BPBorer/RGB2XGA/PCB/RGB2VGA/Manu/3v3 - Err.png

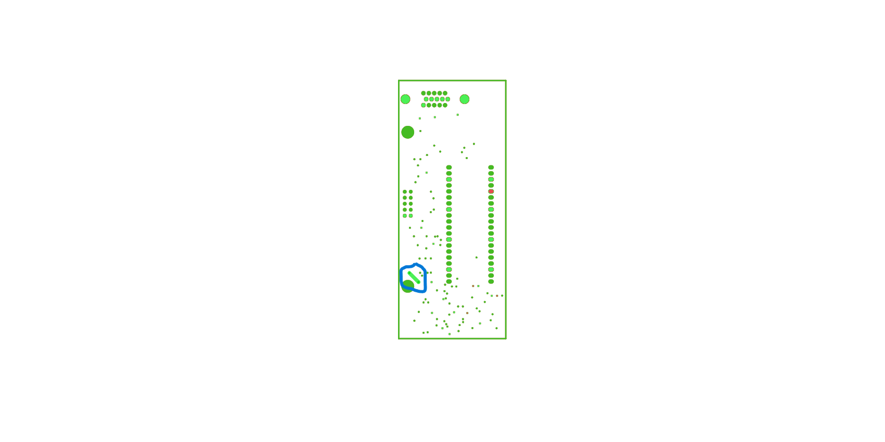
PCB/RGB2VGA/Manu/3v3 - Err.png
